fiveseven808/HueBerry_SmartSwitch/hueBerry Photos/B reel/IMG_20160812_172538.jpg

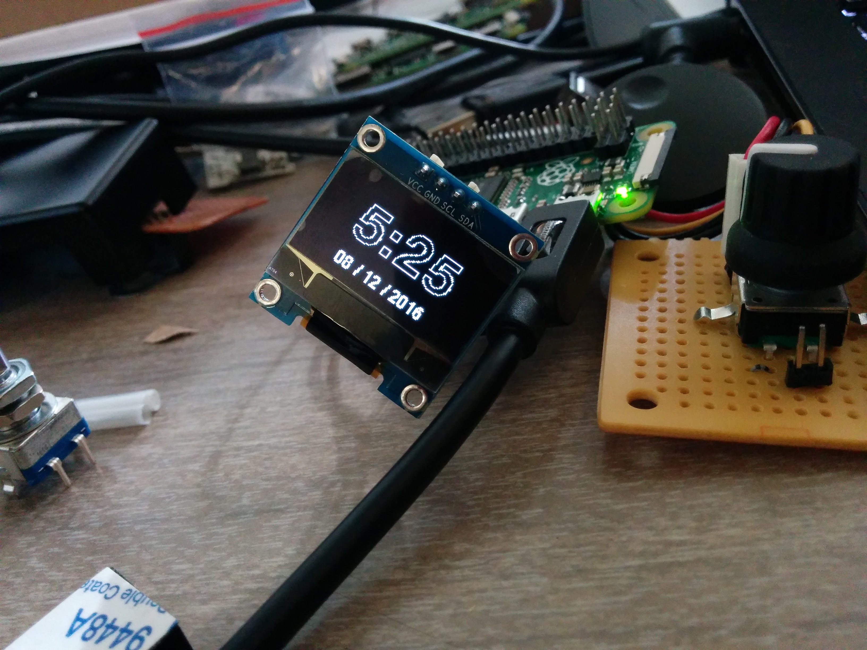
hueBerry Photos/B reel/IMG_20160812_172538.jpg
