fiveseven808/HueBerry_SmartSwitch/hueBerry Photos/B reel/IMG_20161223_000050.jpg

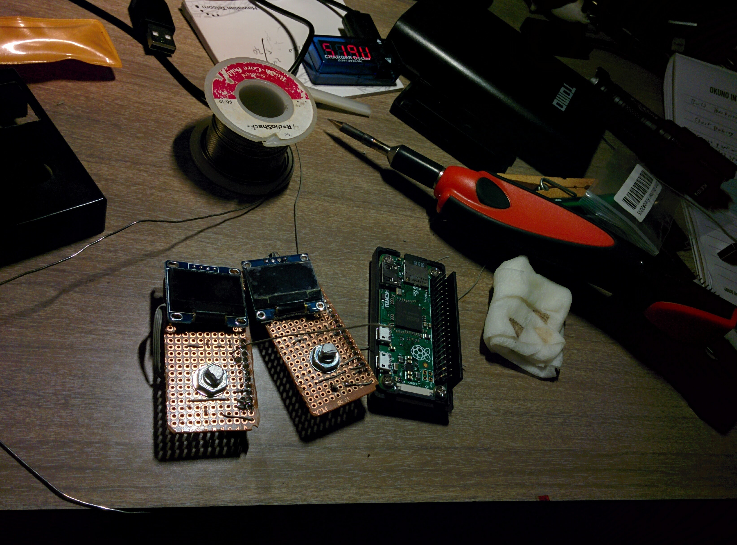
hueBerry Photos/B reel/IMG_20161223_000050.jpg
