fiveseven808/HueBerry_SmartSwitch/hueBerry Photos/B reel/IMG_20161223_075721.jpg

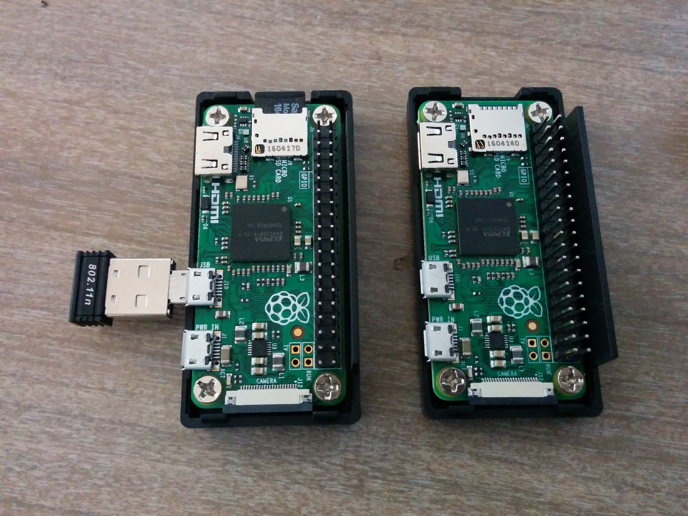
hueBerry Photos/B reel/IMG_20161223_075721.jpg
