fiveseven808/HueBerry_SmartSwitch/hueBerry Photos/Early Prototypes/IMG_20160802_123540.jpg

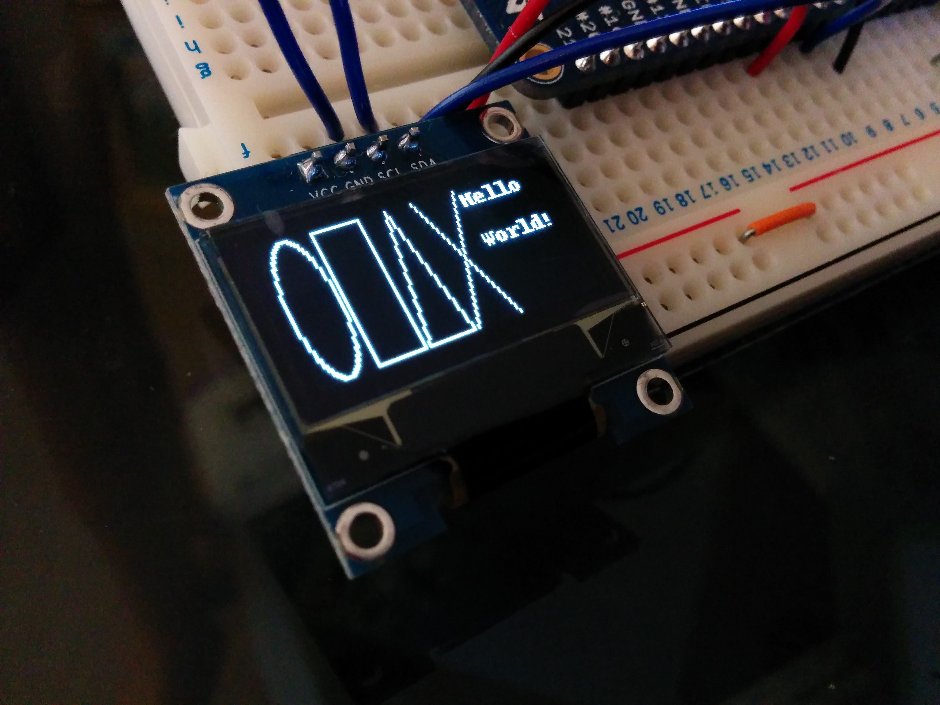
hueBerry Photos/Early Prototypes/IMG_20160802_123540.jpg
