fiveseven808/HueBerry_SmartSwitch/hueBerry Photos/Early Prototypes/IMG_20160812_081227.jpg

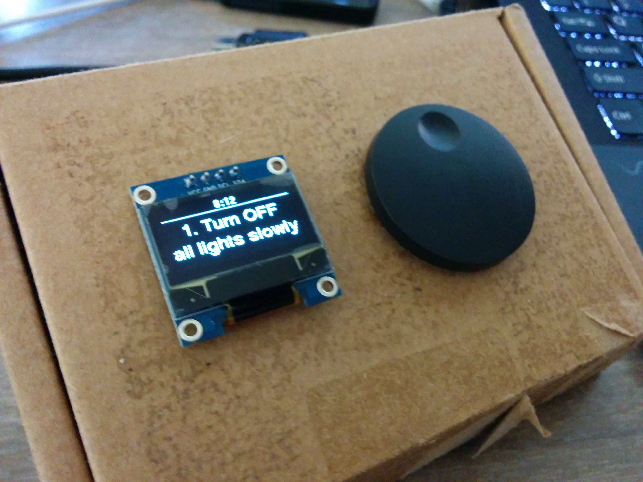
hueBerry Photos/Early Prototypes/IMG_20160812_081227.jpg
