fiveseven808/HueBerry_SmartSwitch/hueBerry Photos/Early Prototypes/IMG_20160812_081231.jpg

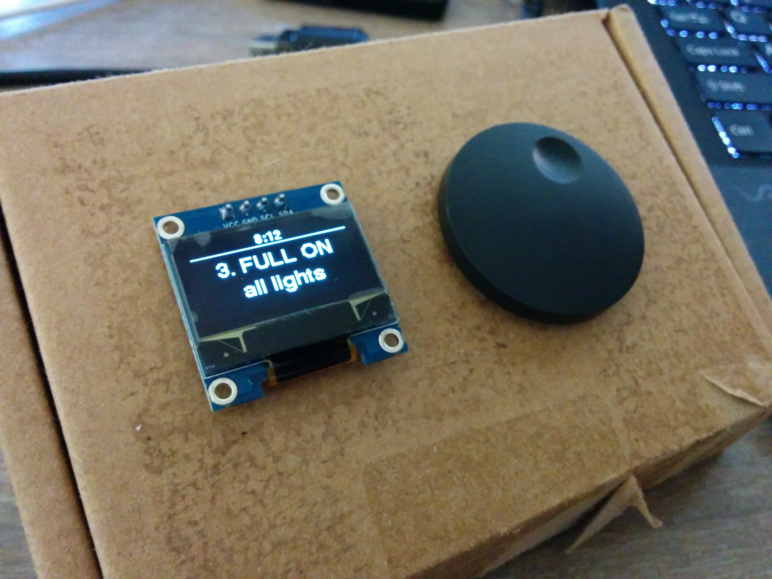
hueBerry Photos/Early Prototypes/IMG_20160812_081231.jpg
