fiveseven808/HueBerry_SmartSwitch/hueBerry Photos/Early Prototypes/IMG_20160812_081238.jpg

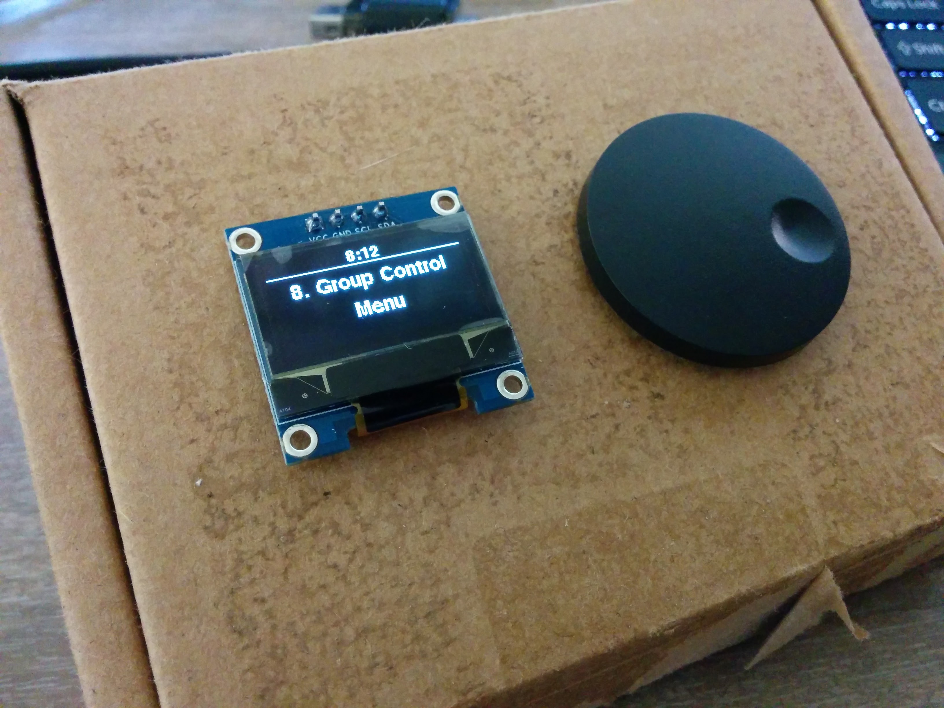
hueBerry Photos/Early Prototypes/IMG_20160812_081238.jpg
