fiveseven808/HueBerry_SmartSwitch/hueBerry Photos/Mistakes/FriedDisplay.jpg

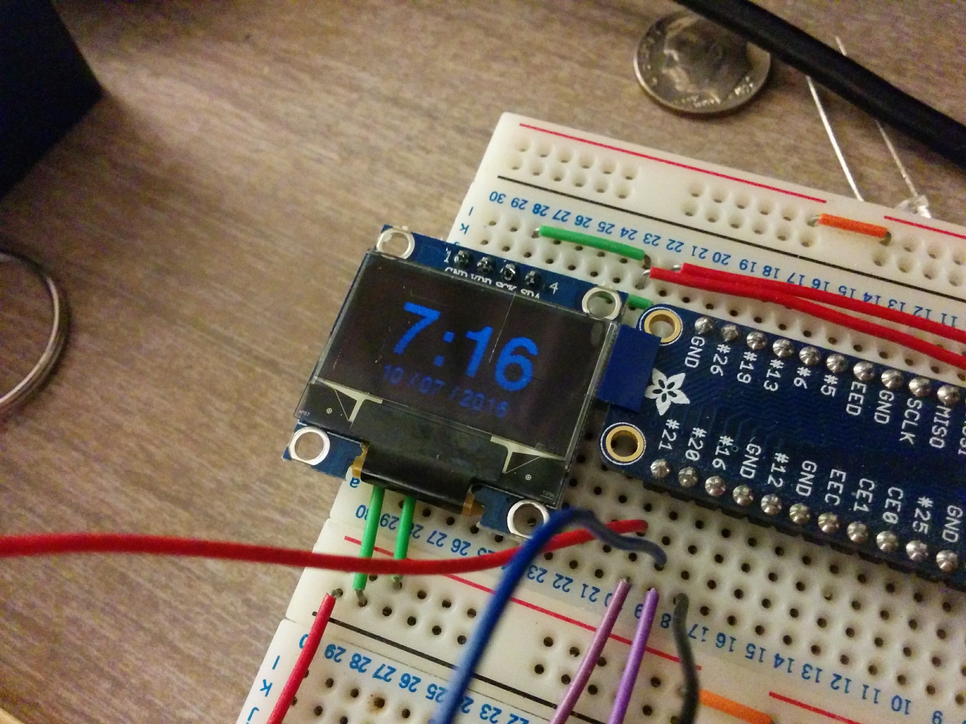
hueBerry Photos/Mistakes/FriedDisplay.jpg
