fiveseven808/HueBerry_SmartSwitch/hueBerry Photos/Mistakes/Notliketheothers.jpg

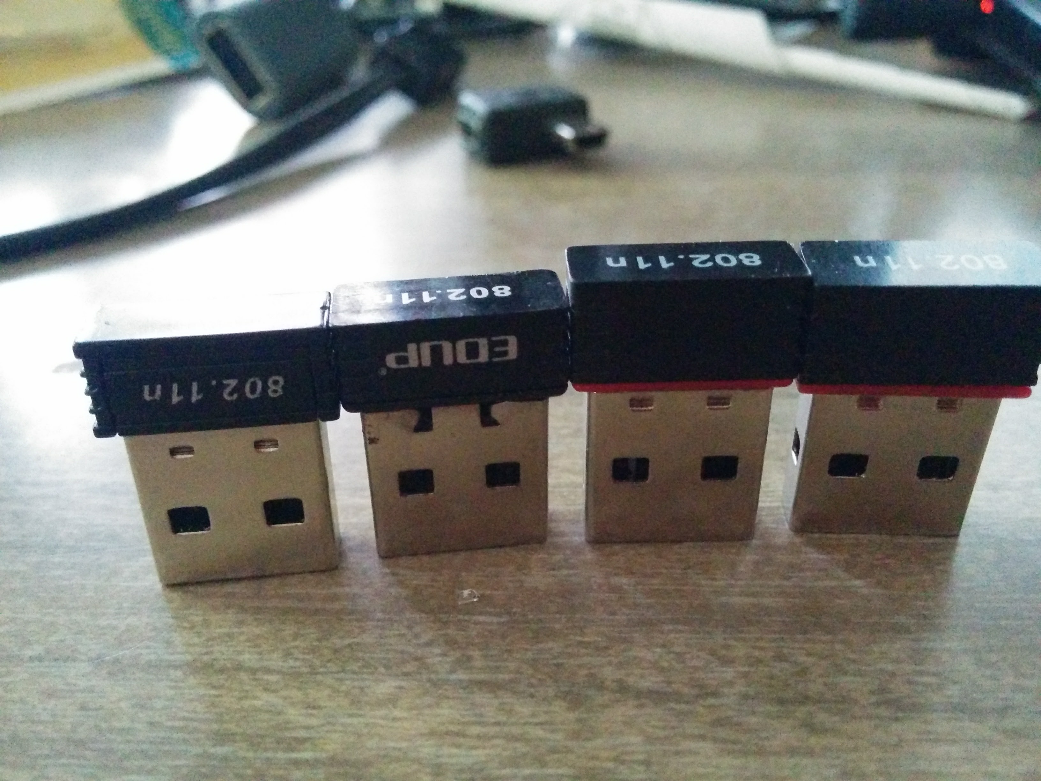
hueBerry Photos/Mistakes/Notliketheothers.jpg
