fiveseven808/HueBerry_SmartSwitch/hueBerry Photos/Construction/IMG_20160925_205256.jpg

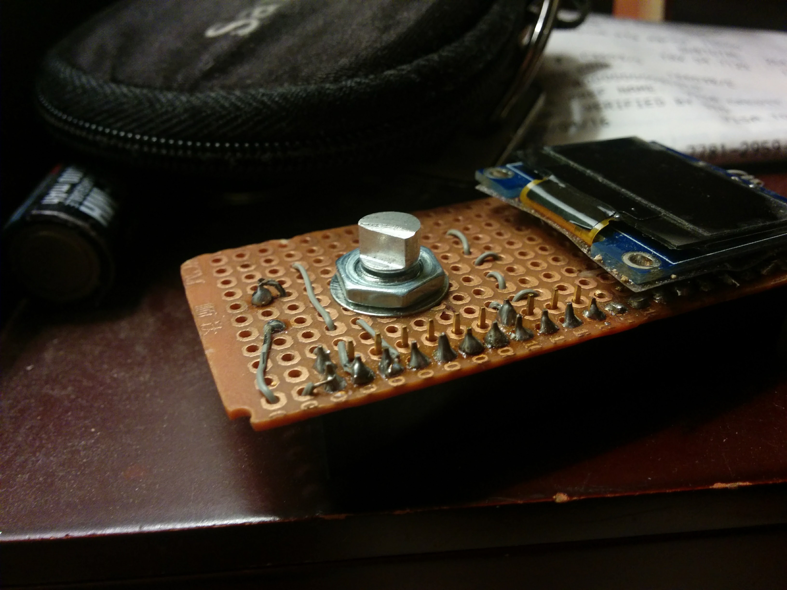
hueBerry Photos/Construction/IMG_20160925_205256.jpg
