fiveseven808/HueBerry_SmartSwitch/hueBerry Photos/Battery Test/IMG_20160907_173014.jpg

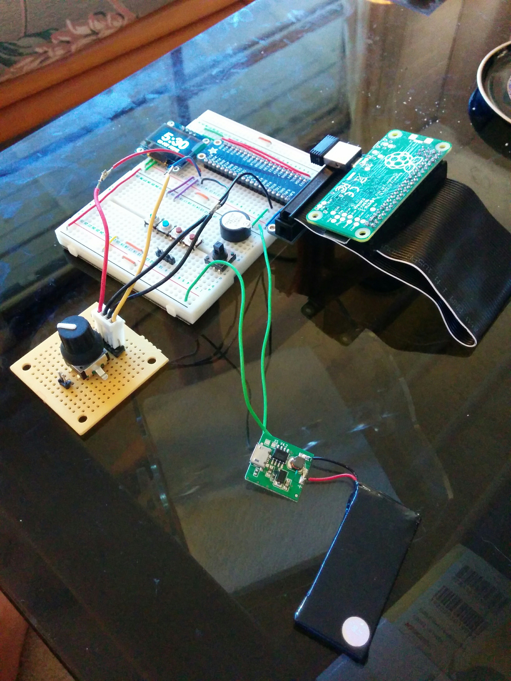
hueBerry Photos/Battery Test/IMG_20160907_173014.jpg
