fiveseven808/HueBerry_SmartSwitch/v032.py

#!/usr/bin/env python
"""
v032
2017 0127
looks like scene saving is working good. Goona go and rearrange my hard scenes to be at the end. 
gonna make custom scenes configurable. make a transition time gathering thing. 
remeoved scene by group since by light is so fast
new process:
    select a scene
        click to activate scene
    hold down for 5 seconds to edit scene
        new menu:
        record scene
        edit transition time
        
    

v031
2017 0126
adding the scene creation function. and replay. 
added 2 ways to do it. using the per light way. both ways work actually. may lead to interesting results
fuck this was difficult 
    

v030 UNTESTED
2017 0118
adding debug statements to each main menu item and light and group action so i can figure out what calvin is doing 

v029 
2017 0116
added keyvalues array to the get_hue_groups function so now we know what the group IDs are specificaLLY 
updated hue control to have full saturation to make it easier to figure out what color you want without having to adjust saturation first. 
updated get_group_names to use the new json scheme 

v028
20170108
removing group 5 from turn on all lights
added debug function and trying to figure out calvins problem
added error handling for hue lights and hue groups function in case calvins thing freaks out 
added proper failed return values so it fails gracefully


v027
20170106 1025
changing display dimish time to 9pm on both date and time

v026
20170103 1117
adding error handlig to the light functions so they dont crash when viewing a group that has no bulbs or a nonexistant group 

v025
20161227 1119
changed the dev info screen to scroll instead of button push. made the hue info screen it's own seperate thing to help curb freezing
added provisions for future upgrades
    - drop upgrade.py in the boot partition, and reboot. should detect and run as root (lol vulnerabilities)

--------------------
bug:
--------------------
philips hue bug
need to repair when no bridge found

search and test auth?
ping on startup?

check for response?
nothing found? 
"""
import os
import os.path
#set working directory to script directory
os.chdir(os.path.dirname(os.path.abspath(__file__)))
os.popen("python splashscreen.py &")
import threading
import time
import Adafruit_SSD1306
import RPi.GPIO as GPIO
from PIL import Image
from PIL import ImageFont
from PIL import ImageDraw
import pigpio
import rotary_encoder
import authenticate
import json
#import subprocess
#import huepi
#figure out how to export this to huepi

global logfile
logfile = "/home/pi/hueberry.log"

menu_timeout = 30 #seconds



#--------------------------------------------------------------------------
def get_group_names():
    result_array = []
    lstate_a = []
    #display_2lines("starting","group names",17)
    #debugmsg("starting curl")
    os.popen("curl -H \"Accept: application/json\" -X GET " + api_url + "/groups  > groups")
    #debugmsg("finished curl")
    #display_2lines("finished","curl",17)
    cmdout = os.popen("cat groups").read()
    #debugmsg(cmdout)
    if not cmdout:
        #print "not brite"
        display_2lines("An error in ","get_group_names",15)
        debugmsg("error in get_group_names probably lost connection to hub")
        time.sleep(2)
        return 0,0,0,0
    #debugmsg("passed ifstatement")
    #print cmdout
    #os.popen("rm groups")
    wat = json.loads(cmdout)
    keyvalues =  wat.keys()
    #print keyvalues
    for x, v  in wat.items():
        result_array.append(wat[x]['name'])
        lstate_a.append(wat[x]['action']['on'])
    num_groups = len(result_array)
    #print num_groups
    #print result_array
    arraysize = len(keyvalues)
    return result_array,num_groups,lstate_a,keyvalues

def get_light_names():
    os.popen("curl -H \"Accept: application/json\" -X GET " + api_url + "/lights  > lights")
    light_names = os.popen("cat lights | grep -P -o '\"name\":\".*?\"' | grep -o ':\".*\"' | tr -d '\"' | tr -d ':'").read()
    if not light_names:
        #print "not brite"
        display_2lines("An error in ","get_light_names",15)
        debugmsg("error in get_light_names probably lost connection to hub")
        time.sleep(2)
        return 0,0,0,0,0
    num_lights = os.popen("cat lights | grep -P -o '\"[0-9]*?\"' | tr -d '\"'").read()
    lstate = os.popen("cat lights | grep -o '\"on\":true,\|\"on\":false,' | tr -d '\"on\":' | tr -d ','").read()
    #os.popen("rm lights")
    name_array = light_names.split('\n')
    num_array = num_lights.split('\n')
    lstate_a = lstate.split('\n')
    total = len(num_array) - 1
    return name_array,num_array,lstate_a,total

    
def get_house_scene_by_light(scenenumber,ltt):
    #Get a fresh groups json file
    display_2lines("Grabbing","Light States",15)
    get_light_names() 
    #display_custom("ran get light names")
    cmdout = os.popen("cat lights").read()
    #os.popen("cat scene_template.py >> custom_scene" + scenenumber + ".py" )
    wat = json.loads(cmdout)
    #display_custom("used jsonloads")
    keyvalues =  wat.keys()
    arraysize = len(keyvalues)
    lstate_a = []
    result_array = []
    bri_array = []
    cmode_array = []
    hue_array = []
    ct_array = []
    sat_array = []
    xy_array = [] 
    #display_custom("blanked varliables")
    #time.sleep(3)
    for x, v  in wat.items():
            result_array.append(wat[x]['name'])
            lstate_a.append(wat[x]['state']['on'])
            #debugmsg v
    display_custom("ran first for")
    #time.sleep(3)
    for x, v  in wat.items():
        display_2lines("Building Array for","Light " + str(x) + " of " + str(len(result_array)),15)
        try:
            bri_array.append(wat[x]['state']['bri'])
        except:
            #debugmsg("errored on item " + x)
            bri_array.append("-1")
        try:
            cmode_array.append(wat[x]['state']['colormode'])
        except:
            #debugmsg("errored on item " + x)
            cmode_array.append("-1")
        try:
            hue_array.append(wat[x]['state']['hue'])
        except:
            #debugmsg("errored on item " + x)
            hue_array.append("-1")
        try:
            ct_array.append(wat[x]['state']['ct'])
        except:
            #debugmsg("errored on item " + x)
            ct_array.append("-1")
        try:
            sat_array.append(wat[x]['state']['sat'])
        except:
            #debugmsg("errored on item " + x)
            sat_array.append("-1")
        try:
            xy_array.append(wat[x]['state']['xy'])
        except:
            #debugmsg("errored on item " + x)
            xy_array.append("-1")
    #time.sleep(3)
    display_2lines("Array","built!",15)
    #print result_array
    #print lstate_a
    #print bri_array
    #print cmode_array
    #print hue_array
    #print ct_array
    #print sat_array
    #print xy_array        
    #ltt = 100
    #api_url = "http://testbridge/something"
    index = 0
    scenefile = str(scenenumber) + "_scene.sh"
    sceneobj = open(scenefile,"w+")
    sceneobj.write("#!/bin/bash\n#\n#This is a scenefile generated by hueBerry\n\n")
    display_2lines("Building","Scene Script!",15)
    while index < len(result_array):    
        scenecmd = "curl --silent -H \"Accept: application/json\" -X PUT --data '{\"on\":" + str(lstate_a[index]).lower() + ",\"bri\":" + str(bri_array[index]) + ",\"sat\":" + str(sat_array[index]) + ",\"xy\":" + str(xy_array[index]) + ",\"transitiontime\":" + str(ltt) + ",\"hue\":" + str(hue_array[index]) + "}' " + api_url + "/lights/" + str(keyvalues[index]) + "/state"
        #display_2lines("Writing","Lights " + str(index + 1) + " of " + str(len(result_array)),15)
        print(scenecmd)
        groupnum = index + 1
        sceneobj.write("echo \"Set Lights " + str(keyvalues[index]) + " = " + str(result_array[index]) + "\"\n")
        sceneobj.write(scenecmd + "\n")
        index += 1
    sceneobj.close
    os.popen("chmod a+x " + scenefile)
    display_2lines("Scenefile","Completed!",15)
    status = "completed"
    return status    
    
def hue_lights(lnum,lon,lbri,lsat,lx,ly,lct,ltt,**options):
    debugmsg("entering hue lights")
    if ('hue' in options):
        result = os.popen("curl --silent -H \"Accept: application/json\" -X PUT --data '{\"on\":" + str(lon) + ",\"bri\":" + str(lbri) + ",\"sat\":" + str(lsat) + ",\"xy\":[" + str(lx) + "," + str(ly) + "],\"transitiontime\":" + str(ltt) + ",\"hue\":" + str(options['hue']) + "}' " + api_url + "/lights/" + str(lnum) + "/state" ).read()
    else:
        result = os.popen("curl --silent -H \"Accept: application/json\" -X PUT --data '{\"on\":" + str(lon) + ",\"bri\":" + str(lbri) + ",\"sat\":" + str(lsat) + ",\"xy\":[" + str(lx) + "," + str(ly) + "],\"transitiontime\":" + str(ltt) + ",\"ct\":" + str(lct) + "}' " + api_url + "/lights/" + str(lnum) + "/state" ).read()
    debugmsg(result)    
    if not result:
        #print "not brite"
        display_2lines("An error in ","hue_lights",17)
        time.sleep(2)
        return
    print(result)
    return result

def hue_groups(lnum,lon,lbri,lsat,lx,ly,lct,ltt,**options):
    debugmsg("entering hue groups")
    if ('hue' in options):
        #debugmsg("hue and before result")
        result = os.popen("curl --silent -H \"Accept: application/json\" -X PUT --data '{\"on\":" + str(lon) + ",\"bri\":" + str(lbri) + ",\"sat\":" + str(lsat) + ",\"xy\":[" + str(lx) + "," + str(ly) + "],\"transitiontime\":" + str(ltt) + ",\"hue\":" + str(options['hue']) + "}' " + api_url + "/groups/" + str(lnum) + "/action" ).read()
        #debugmsg("hue and after result")
    else:
        #debugmsg("everything else and before result")
        result = os.popen("curl -s -m 1 -H \"Accept: application/json\" -X PUT --data '{\"on\":" + str(lon) + ",\"bri\":" + str(lbri) + ",\"sat\":" + str(lsat) + ",\"xy\":[" + str(lx) + "," + str(ly) + "],\"transitiontime\":" + str(ltt) + ",\"ct\":" + str(lct) + "}' " + api_url + "/groups/" + str(lnum) + "/action").read()
        #debugmsg("everything else and after result")
    debugmsg(result)
    if not result:
        #print "not brite"
        display_2lines("An error in ","hue_groups",17)
        time.sleep(2)
        return
    #print(result)
    #debugmsg("printed result")
    return result

#------------------------------------------------------------------------------------  
#   This function is the main menu for any light adjustment 
#   It displays lights or groups in the hue system and then allows you to control 
#       brightness, color temp, hue, and saturation in a fairly intuitive manner
#
#   Usage:
#       Specify "g" or "l" depending if you want to control a group or a light
#       Quick Push:
#           Brightness or exit
#       Long push:
#           CT adjustment or move to next option
#
#   Displays: 
#       Group or Light name as you scroll around. Allows you to change most attributes of the light
#------------------------------------------------------------------------------------
def light_control(mode):
    if (mode == "g"):
        display_custom("loading groups...")
        name_array,total,lstate_a,keyvalues = get_group_names()
    elif (mode == "l"):
        display_custom("loading lights...")
        name_array,num_lights,lstate_a,total = get_light_names()
    global pos
    old_display = 0
    refresh = 1
    exitvar = False
    menudepth = total + 1
    while exitvar == False:
        if(pos > menudepth):
            pos = menudepth
        elif(pos < 1):
            pos = 1
        display = pos

        #Display Selected Menu
        if (old_display != display or refresh == 1):
            if(display <= total):
                display_3lines(str(display) + ". " + str(name_array[display-1]),"Control","ON: " + str(lstate_a[display-1]),11,offset = 15)
            else:
                display_2lines("Back","One Level",17)
            old_display = display
            refresh = 0
        else:
            time.sleep(0.005)

        # Poll button press and trigger action based on current display
        if(not GPIO.input(21)):
            if(display <= total):
                ctmode = 0
                huemode = 0
                prev_mills = int(round(time.time() * 1000))
                while(not GPIO.input(21)):
                    mills = int(round(time.time() * 1000))
                    millsdiff = mills - prev_mills
                    if(millsdiff < 500):
                        display_custom("hold for ct...")
                    elif(millsdiff >= 500):
                        ctmode = 1
                        break
                while(not GPIO.input(21)):
                    display_custom("entering ct...")
                if(ctmode == 0):
                    if(mode == "g"):
                        g_control(keyvalues[display-1])
                        prev_mills = int(round(time.time() * 1000))
                        while(not GPIO.input(21)):
                            mills = int(round(time.time() * 1000))
                            millsdiff = mills - prev_mills
                            if(millsdiff < 500):
                                display_custom("hold for ct...")
                            elif(millsdiff >= 500):
                                ctmode = 1
                                break
                        if (ctmode ==0):
                            display_custom("returning...")
                        else:
                            while(not GPIO.input(21)):
                                display_custom("entering ct...")
                    elif(mode == "l"):
                        l_control(num_lights[display-1])
                        prev_mills = int(round(time.time() * 1000))
                        while(not GPIO.input(21)):
                            mills = int(round(time.time() * 1000))
                            millsdiff = mills - prev_mills
                            if(millsdiff < 500):
                                display_custom("hold for ct...")
                            elif(millsdiff >= 500):
                                ctmode = 1
                                break
                        if (ctmode ==0):
                            display_custom("returning...")
                        else:
                            while(not GPIO.input(21)):
                                display_custom("entering ct...")
                        

                if(ctmode == 1):
                    if(mode == "g"):
                        ct_control(keyvalues[display-1],"g")
                        prev_mills = int(round(time.time() * 1000))
                        while(not GPIO.input(21)):
                            mills = int(round(time.time() * 1000))
                            millsdiff = mills - prev_mills
                            if(millsdiff < 500):
                                display_custom("hold for hue...")
                            elif(millsdiff >= 500):
                                huemode = 1
                                break
                        if (huemode == 1):
                            hue_control(keyvalues[display-1],"g")
                            huemode = 0
                        elif(huemode ==0):
                            display_custom("returning...")
                        prev_mills = int(round(time.time() * 1000))
                        while(not GPIO.input(21)):
                            mills = int(round(time.time() * 1000))
                            millsdiff = mills - prev_mills
                            if(millsdiff < 500):
                                display_custom("hold for sat...")
                            elif(millsdiff >= 500):
                                huemode = 1
                                break
                        if (huemode == 1):
                            sat_control(keyvalues[display-1],"g")
                        elif(huemode ==0):
                            display_custom("returning...")
                           
                    elif(mode == "l"):
                        ct_control(num_lights[display-1],"l") 
                        prev_mills = int(round(time.time() * 1000))
                        while(not GPIO.input(21)):
                            mills = int(round(time.time() * 1000))
                            millsdiff = mills - prev_mills
                            if(millsdiff < 500):
                                display_custom("hold for hue...")
                            elif(millsdiff >= 500):
                                huemode = 1
                                break
                        if (huemode == 1):
                            hue_control(num_lights[display-1],"l")
                            huemode = 0
                        elif(huemode ==0):
                            display_custom("returning...")
                        prev_mills = int(round(time.time() * 1000))
                        while(not GPIO.input(21)):
                            mills = int(round(time.time() * 1000))
                            millsdiff = mills - prev_mills
                            if(millsdiff < 500):
                                display_custom("hold for sat...")
                            elif(millsdiff >= 500):
                                huemode = 1
                                break
                        if (huemode == 1):
                            sat_control(num_lights[display-1],"l")
                        elif(huemode ==0):
                            display_custom("returning...")
                if(mode == "g"):
                    name_array,total,lstate_a,keyvalues = get_group_names()
                elif(mode == "l"):
                    name_array,num_lights,lstate_a,total = get_light_names()
                refresh = 1 
                pos = display
            else:
                time.sleep(0.25)
                exitvar = True
            time.sleep(0.01)
            #prev_millis = int(round(time.time() * 1000))
    return
    


def g_control(group):
    display_custom("loading brightness...")
    os.popen("curl -H \"Accept: application/json\" -X GET " + api_url + "/groups/" + str(group) + " > brite")
    brite = os.popen("cat brite | grep -o '\"bri\":[0-9]*' | grep -o ':.*' | tr -d ':'").read()
    os.popen("rm brite")
    if not brite:
        #print "not brite"
        display_2lines("No devices","in group",17)
        time.sleep(3)
        return
    #else: 
    #    print "guess it was brite"
    brite = int(brite)      #make integer
    if brite < 10 and brite >= 0:
        brite = 10

    brite = brite/10        #trim it down to 25 values
    brite = int(brite)      #convert the float down to int agian
    global pos
    pos = brite
    exitvar = False
    max_rot_val = 25
    bri_pre = pos * 10
    refresh = 1
    prev_mills = 0 
    while exitvar == False:
        if(pos > max_rot_val):
            pos = max_rot_val
        elif(pos < 0):
            pos = 0
        mills = int(round(time.time() * 1000))
        millsdiff = mills - prev_mills
        rot_bri = pos * 10
        if(bri_pre != rot_bri or refresh ==  1 ):
            display_2lines("Group " + str(group),"Bri: " + str(int(rot_bri/2.5)) + "%",17)
            refresh = 0
        if rot_bri <= 0 and rot_bri != bri_pre:
            #hue_groups(lnum = group,lon = "false",lbri = rot_bri,lsat = "-1",lx = "-1",ly = "-1",ltt = "5", lct = "-1")
            huecmd = threading.Thread(target = hue_groups, kwargs={'lnum':group,'lon':"false",'lbri':rot_bri,'lsat':"-1",'lx':"-1",'ly':"-1",'ltt':"5",'lct':"-1"})
            huecmd.start()
            bri_pre = rot_bri
        elif(rot_bri != bri_pre and millsdiff > 200):
            #hue_groups(lnum = group,lon = "true",lbri = rot_bri,lsat = "-1",lx = "-1",ly = "-1",ltt = "5", lct = "-1")
            huecmd = threading.Thread(target = hue_groups, kwargs={'lnum':group,'lon':"true",'lbri':rot_bri,'lsat':"-1",'lx':"-1",'ly':"-1",'ltt':"5",'lct':"-1"})
            huecmd.start()
            bri_pre = rot_bri
            prev_mills = mills
        elif(millsdiff > 200): 
            prev_mills = mills
            
        if(not GPIO.input(21)):
            exitvar = True
        time.sleep(0.01)

#------------------------------------------------------------------------------------  
#   This function controls the color temperature of a light or group
#   Usage:
#       Specify the group or light ID in device
#       Specify "g" or "l" depending if you want to control a group or a light
#
#   Displays: 
#       Group or Light ID and current CT level in Kelvin 
#------------------------------------------------------------------------------------
def ct_control(device,mode):
    display_custom("loading ct...")
    if (mode == "g"):
        os.popen("curl -H \"Accept: application/json\" -X GET " + api_url + "/groups/" + str(device) + " > brite")
    elif (mode == "l"):
        os.popen("curl -H \"Accept: application/json\" -X GET " + api_url + "/lights/" + str(device) + " > brite")
    brite = os.popen("cat brite | grep -o '\"ct\":[0-9]*' | grep -o ':.*' | tr -d ':'").read()
    os.popen("rm brite")
    if not brite:
        #print "not brite"
        display_2lines("No devices","in group",17)
        time.sleep(3)
        return
    bri_length = len(brite)
    print bri_length
    if (bri_length > 0):
        brite = int(brite)      #make integer
        brite = 25-((brite - 153) / 14)
        brite = int(brite)      #convert the float down to int agian
    else:
        if (mode == "l"):
            display_custom("Light " + str(device) + " isn't CT-able")
        elif (mode == "g"):
            display_custom("Group " + str(device) + " isn't CT-able")
        time.sleep(.5)
        return
    global pos
    pos = brite
    exitvar = False
    max_rot_val = 25
    bri_pre = ((25-pos) * 14) + 153
    refresh = 1
    prev_mills = 0 
    while exitvar == False:
        if(pos > max_rot_val):
            pos = max_rot_val
        elif(pos < 0):
            pos = 0
        mills = int(round(time.time() * 1000))
        millsdiff = mills - prev_mills
        rot_bri = ((25-pos) * 14) + 153
        if(bri_pre != rot_bri or refresh ==  1 ):
            tempcalc = ((-12.968*rot_bri)+8484)/100
            tempcalc = (round(tempcalc))*100
            tempcalc = int(tempcalc)
            if(mode == "g"):
                display_2lines("Group " + str(device),"CT: " + str(int(tempcalc)) + "K",17)
            elif(mode == "l"):
                display_2lines("Light " + str(device),"CT: " + str(int(tempcalc)) + "K",17)
            refresh = 0
        if(rot_bri != bri_pre and millsdiff > 250):
            if(rot_bri > 500):
                rotbri = 500
            if(mode == "g"):
                #hue_groups(lnum = device,lon = "true",lbri = "-1",lsat = "-1",lx = "-1",ly = "-1",ltt = "5", lct = rot_bri)
                huecmd = threading.Thread(target = hue_groups, kwargs={'lnum':device,'lon':"true",'lbri':"-1",'lsat':"-1",'lx':"-1",'ly':"-1",'ltt':"5",'lct':rot_bri})
                huecmd.start()
            elif(mode == "l"):
                #hue_lights(lnum = device,lon = "true",lbri = "-1",lsat = "-1",lx = "-1",ly = "-1",ltt = "5", lct = rot_bri)
                huecmd = threading.Thread(target = hue_lights, kwargs={'lnum':device,'lon':"true",'lbri':"-1",'lsat':"-1",'lx':"-1",'ly':"-1",'ltt':"5",'lct':rot_bri})
                huecmd.start()
            bri_pre = rot_bri
            print rot_bri
            prev_mills = mills
        elif(millsdiff > 250): 
            prev_mills = mills
            
        if(not GPIO.input(21)):
            exitvar = True
        time.sleep(0.01)

def hue_control(device,mode):
    while(not GPIO.input(21)):
        display_custom("loading hue...")
    if (mode == "g"):
        os.popen("curl -H \"Accept: application/json\" -X GET " + api_url + "/groups/" + str(device) + " > brite")
    elif (mode == "l"):
        os.popen("curl -H \"Accept: application/json\" -X GET " + api_url + "/lights/" + str(device) + " > brite")
    brite = os.popen("cat brite | grep -o '\"hue\":[0-9]*' | grep -o ':.*' | tr -d ':'").read()
    os.popen("rm brite")
    if not brite:
        #print "not brite"
        display_2lines("No devices","in group",17)
        time.sleep(3)
        return
    bri_length = len(brite)
    print bri_length
    if (bri_length > 0):
        brite = int(brite)      #make integer
        brite = brite / 1310
        brite = int(round(brite))      #convert the float down to int agian
    else:
        print "something happened"
        if (mode == "l"):
            display_custom("Light " + str(device) + " isn't HUE-able")
        elif (mode == "g"):
            display_custom("Group " + str(device) + " isn't HUE-able")
        time.sleep(.5)
        return
    global pos
    pos = brite
    exitvar = False
    max_rot_val = 50
    bri_pre = brite
    refresh = 1
    prev_mills = 0 
    while exitvar == False:
        if(pos > max_rot_val):
            pos = 0
        elif(pos < 0):
            pos = max_rot_val   
        mills = int(round(time.time() * 1000))
        millsdiff = mills - prev_mills
        rot_bri = pos * 1310
        if(bri_pre != rot_bri or refresh ==  1 ):
            if(mode == "g"):
                display_2lines("Group " + str(device),"Hue: " + str(int(rot_bri)) ,17)
            elif(mode == "l"):
                display_2lines("Light " + str(device),"Hue: " + str(int(rot_bri)) ,17)
            refresh = 0
        if(rot_bri != bri_pre and millsdiff > 250):
            if(mode == "g"):
                #hue_groups(lnum = device,lon = "true",lbri = "-1",lsat = "-1",lx = "-1",ly = "-1",ltt = "5", lct = "-1", hue = rot_bri)
                huecmd = threading.Thread(target = hue_groups, kwargs={'lnum':device,'lon':"true",'lbri':"-1",'lsat':"250",'lx':"-1",'ly':"-1",'ltt':"5",'lct':"-1",'hue':rot_bri})
                huecmd.start()
            elif(mode == "l"):
                #hue_lights(lnum = device,lon = "true",lbri = "-1",lsat = "-1",lx = "-1",ly = "-1",ltt = "5", lct = "-1", hue = rot_bri)
                huecmd = threading.Thread(target = hue_lights, kwargs={'lnum':device,'lon':"true",'lbri':"-1",'lsat':"250",'lx':"-1",'ly':"-1",'ltt':"5",'lct':"-1",'hue':rot_bri})
                huecmd.start()
            bri_pre = rot_bri
            print rot_bri
            prev_mills = mills
        elif(millsdiff > 250): 
            prev_mills = mills
            
        if(not GPIO.input(21)):
            exitvar = True
        time.sleep(0.01)
        
def sat_control(device,mode):
    while(not GPIO.input(21)):
        display_custom("loading sat...")
    if (mode == "g"):
        os.popen("curl -H \"Accept: application/json\" -X GET " + api_url + "/groups/" + str(device) + " > brite")
    elif (mode == "l"):
        os.popen("curl -H \"Accept: application/json\" -X GET " + api_url + "/lights/" + str(device) + " > brite")
    brite = os.popen("cat brite | grep -o '\"sat\":[0-9]*' | grep -o ':.*' | tr -d ':'").read()
    os.popen("rm brite")
    if not brite:
        #print "not brite"
        display_2lines("No devices","in group",17)
        time.sleep(3)
        return
    bri_length = len(brite)
    print bri_length
    if (bri_length > 0):
        brite = int(brite)      #make integer
        brite = brite / 10
        brite = int(round(brite))      #convert the float down to int agian
    else:
        if (mode == "l"):
            display_custom("Light " + str(device) + " isn't SAT-able")
        elif (mode == "g"):
            display_custom("Group " + str(device) + " isn't SAT-able")
        time.sleep(.5)
        return
    global pos
    pos = brite
    exitvar = False
    max_rot_val = 25
    bri_pre = brite
    refresh = 1
    prev_mills = 0 
    while exitvar == False:
        if(pos > max_rot_val):
            pos = max_rot_val
        elif(pos < 0):
            pos = 0
        mills = int(round(time.time() * 1000))
        millsdiff = mills - prev_mills
        rot_bri = pos * 10
        if(bri_pre != rot_bri or refresh ==  1 ):
            if(mode == "g"):
                display_2lines("Group " + str(device),"Sat: " + str(int(rot_bri)) ,17)
            elif(mode == "l"):
                display_2lines("Light " + str(device),"Sat: " + str(int(rot_bri)) ,17)
            refresh = 0
        if(rot_bri != bri_pre and millsdiff > 250):
            if(mode == "g"):
                #hue_groups(lnum = device,lon = "true",lbri = "-1",lsat = rot_bri,lx = "-1",ly = "-1",ltt = "5", lct = "-1")
                huecmd = threading.Thread(target = hue_groups, kwargs={'lnum':device,'lon':"true",'lbri':"-1",'lsat':rot_bri,'lx':"-1",'ly':"-1",'ltt':"5",'lct':"-1"})
                huecmd.start()
            elif(mode == "l"):
                #hue_lights(lnum = device,lon = "true",lbri = "-1",lsat = rot_bri,lx = "-1",ly = "-1",ltt = "5", lct = "-1")
                huecmd = threading.Thread(target = hue_lights, kwargs={'lnum':device,'lon':"true",'lbri':"-1",'lsat':rot_bri,'lx':"-1",'ly':"-1",'ltt':"5",'lct':"-1"})
                huecmd.start()
            bri_pre = rot_bri
            print rot_bri
            prev_mills = mills
        elif(millsdiff > 250): 
            prev_mills = mills
            
        if(not GPIO.input(21)):
            exitvar = True
        time.sleep(0.01)
        
def l_control(light):
    display_custom("loading brightness...")
    os.popen("curl -H \"Accept: application/json\" -X GET  "+ api_url + "/lights/" + str(light) + " > brite")
    brite = os.popen("cat brite | grep -o '\"bri\":[0-9]*' | grep -o ':.*' | tr -d ':'").read()
    os.popen("rm brite")
    if not brite:
        #print "not brite"
        display_2lines("No devices","in lights",17)
        time.sleep(3)
        return
    brite = int(brite)      #make integer
    if brite < 10 and brite >= 0:
        brite = 10

    brite = brite/10        #trim it down to 25 values
    brite = int(brite)      #convert the float down to int agian
    global pos
    pos = brite
    exitvar = False
    max_rot_val = 25
    bri_pre = pos * 10
    refresh = 1
    prev_mills = 0 
    while exitvar == False:
        if(pos > max_rot_val):
            pos = max_rot_val
        elif(pos < 0):
            pos = 0
        mills = int(round(time.time() * 1000))
        millsdiff = mills - prev_mills
        rot_bri = pos * 10
        if(bri_pre != rot_bri or refresh == 1 ):
            display_2lines("Light " + str(light),"Bri: " + str(int(rot_bri/2.5)) + "%",17)
            refresh = 0 
        if rot_bri <= 0 and rot_bri != bri_pre:
            huecmd = threading.Thread(target = hue_lights, kwargs={'lnum':light,'lon':"false",'lbri':rot_bri,'lsat':"-1",'lx':"-1",'ly':"-1",'ltt':"5",'lct':"-1"})
            huecmd.start()
            bri_pre = rot_bri
        elif(rot_bri != bri_pre and millsdiff > 100):
            huecmd = threading.Thread(target = hue_lights, kwargs={'lnum':light,'lon':"true",'lbri':rot_bri,'lsat':"-1",'lx':"-1",'ly':"-1",'ltt':"5",'lct':"-1"})
            huecmd.start()
            bri_pre = rot_bri
            prev_mills = mills
        elif(millsdiff > 100): 
            prev_mills = mills

        if(not GPIO.input(21)):
            exitvar = True
        time.sleep(0.01)
#-------------------------------------------------------------------
#---------------Settings Menu and stuff-----------------------------
#-------------------------------------------------------------------
def pair_hue_bridge():
    pos = 0
    if os.path.isfile('./auth.json') == False:
        while True:
            display_3lines("Attempting Link","Push Bridge button" ,"Then push this button",11,offset = 15)
            if(not GPIO.input(21)):
                break
        display_custom("doing a thing...") 
        ip = authenticate.search_for_bridge()
        authenticate.authenticate('hueBerry',ip)
        authenticate.load_creds()
        api_key = authenticate.api_key
        bridge_ip = authenticate.bridge_ip
        display_2lines("Link Successful",bridge_ip,12)
        time.sleep(1)
    else:
        authenticate.load_creds()
        api_key = authenticate.api_key
        bridge_ip = authenticate.bridge_ip
        api_url = 'http://%s/api/%s' % (bridge_ip,api_key)
        display_2lines("Already Paired!",bridge_ip,12)
        time.sleep(1)
        
def devinfo_screen():
    time.sleep(.25)
    global pos
    pos = 0
    old_display = 0
    exitvar = False
    menudepth = 4
    refresh = 1 
    
    ipaddress = os.popen("ifconfig wlan0 | grep 'inet addr' | awk -F: '{print $2}' | awk '{print $1}'").read()
    ssid = os.popen("iwconfig wlan0 | grep 'ESSID' | awk '{print $4}' | awk -F\\\" '{print $2}'").read()
    ipaddress_0 = os.popen("ifconfig eth0 | grep 'inet addr' | awk -F: '{print $2}' | awk '{print $1}'").read()
    ipaddress_1 = os.popen("ifconfig eth1 | grep 'inet addr' | awk -F: '{print $2}' | awk '{print $1}'").read()
    while exitvar == False:
        if(pos > menudepth):
            pos = menudepth
        elif(pos < 1):
            pos = 1
        display = pos

        #Display Selected Menu
        if (old_display != display or refresh == 1):
            if(display == 1):
                display_3lines("hueBerry IP: " + str(ipaddress),"Bridge IP: " + str(bridge_ip) ,"WLAN SSID: " + str(ssid),9,offset = 15)
            elif(display == 2):
                display_3lines("eth0 IP: " + str(ipaddress_0),"eth1 IP: " + str(ipaddress_1) ,"blah",9,offset = 15)
            elif(display == 3):
                display_2lines("Get hue Hub","Info",17)
            else:
                display_2lines("Back to","Settings Menu",17)
            old_display = display
            refresh = 0 
        else:
            time.sleep(0.005)

        # Poll button press and trigger action based on current display
        if(not GPIO.input(21)):
            if(display == 1):
                ipaddress = os.popen("ifconfig wlan0 | grep 'inet addr' | awk -F: '{print $2}' | awk '{print $1}'").read()
                ssid = os.popen("iwconfig wlan0 | grep 'ESSID' | awk '{print $4}' | awk -F\\\" '{print $2}'").read()
                display_3lines("hueBerry IP: " + str(ipaddress),"Bridge IP: " + str(bridge_ip) ,"WLAN SSID: " + str(ssid),9,offset = 15)
            elif(display == 2):
                ipaddress_0 = os.popen("ifconfig eth0 | grep 'inet addr' | awk -F: '{print $2}' | awk '{print $1}'").read()
                ipaddress_1 = os.popen("ifconfig eth1 | grep 'inet addr' | awk -F: '{print $2}' | awk '{print $1}'").read()
                display_3lines("eth0 IP: " + str(ipaddress_0),"eth1 IP: " + str(ipaddress_1) ,"blah",9,offset = 15)
            elif(display == 3):
                get_hue_devinfo()
            else:
                time.sleep(0.25)
                exitvar = True
            refresh = 1
            pos = display
            while(not GPIO.input(21)):
                time.sleep(0.01)
            #prev_millis = int(round(time.time() * 1000))
    return
    
def get_hue_devinfo():
    display_custom("loading groups...")
    name_array,total,lstate_a,keyvalues = get_group_names()
    maxgroupid = keyvalues[total-1]
    display_custom("loading lights...")
    name_array,num_lights,lstate_a,total = get_light_names()
    maxlightid = num_lights[total-1]
    display_3lines("Max Light ID: " + str(maxlightid),"Max Group ID: " + str(maxgroupid) ,"something something",9,offset = 15)
    while True:
        time.sleep(0.01)
        if(not GPIO.input(21)):
            break
            
def shutdown_hueberry():
    display_3lines("Shutting down now...","Don't remove power" ,"Until Display is off",11,offset = 15)
    os.popen("sudo shutdown now")
    while True:
        time.sleep(1)
        
def restart_hueberry():
    display_3lines("Restarting now...","Don't remove power" ,"Please Wait",11,offset = 15)
    os.popen("sudo shutdown -r now")
    while True:
        time.sleep(1)
        
def flashlight_mode():
    while True:
        if(GPIO.input(21)):
            break
    draw.rectangle((0,0,width,height), outline=0, fill=1)
    disp.image(image)
    disp.display()
    while True:
        if(not GPIO.input(21)):
            break
        time.sleep(0.1)

def wifi_settings():
    display_custom("scanning for wifi...")
    global pos
    pos = 0
    timeout = 0 
    os.popen("wpa_cli scan")
    os.popen("wpa_cli scan_results | grep WPS | sort -r -k3 > /tmp/wifi")
    ssids = os.popen("cat /tmp/wifi | awk '{print $5}'").read()
    powers = os.popen("cat /tmp/wifi | awk '{print $3}'").read()
    macs = os.popen("cat /tmp/wifi | awk '{print $1}'").read()
    ssid_array = ssids.split('\n')
    mac_array = macs.split('\n')
    p_array = powers.split('\n')
    total = len(ssid_array) - 1
    menudepth = total + 1
    while True:
        if(pos > menudepth):
            pos = menudepth
        elif(pos < 0):
            pos = 0
        display = pos

        #Display Selected Menu
        if(display == 0):
            display_3lines("Scroll to see","Avaliable [WPS]" ,"SSIDs",11,offset = 15)
        elif(display <= total):
            display_3lines(str(display) + ". " + str(ssid_array[display-1]),"Signal: " + str(p_array[display-1]),"Connect ?",11,offset = 15)
        else:
            display_2lines("Back to","Settings Menu",17)

        # Poll button press and trigger action based on current display
        if(not GPIO.input(21)):
            if(display <= total and display > 0):
                timeout = 0
                display_3lines("Connecting To:",str(ssid_array[display-1]) ,"Push WPS button then click ",9,offset = 15)
                while True:
                    if(GPIO.input(21)):
                        break
                while True:
                    display_3lines("Connecting To:",str(ssid_array[display-1]) ,"Push WPS button then click ",9,offset = 15)
                    if(not GPIO.input(21)):
                        time.sleep(0.01)
                        break
                display_2lines("Pairing","Please Wait...",15)
                os.popen("wpa_cli wps_pbc " + str(mac_array[display-1]))
                # display_custom("something")
                time.sleep(2)
                while(timeout <= 60):
                    ipaddress = os.popen("ifconfig wlan0 | grep 'inet addr' | awk -F: '{print $2}' | awk '{print $1}'").read()
                    addr_len = len(ipaddress)
                    display_3lines("Waiting for an IP",".","IP: " + str(ipaddress),11,offset = 15)
                    if(addr_len > 4 ):
                        print("i have an ip address!!! at " + str(ipaddress))
                        break
                    timeout += 1
                    time.sleep(.25)
                    display_3lines("Waiting for an IP",". .","IP: " + str(ipaddress),11,offset = 15)
                    time.sleep(.25)
                    display_3lines("Waiting for an IP",". . .","IP: " + str(ipaddress),11,offset = 15)
                    time.sleep(.5)
                    if(not GPIO.input(21)):
                        break
                if(timeout >= 300):
                    display_2lines("Connection failed...","Try again",15)
                elif(addr_len < 4):
                    display_2lines("Connection canceled...","Try again",15)
                else:
                    display_2lines("Success!!!","IP: " + str(ipaddress),13)
                time.sleep(5)
            else:
                time.sleep(0.25)
                break
            time.sleep(0.01)
    
        
def settings_menu():
    time.sleep(.25)
    global pos
    pos = 0
    old_display = 0
    exitvar = False
    menudepth = 7
    refresh = 1 
    while exitvar == False:
        if(pos > menudepth):
            pos = menudepth
        elif(pos < 1):
            pos = 1
        display = pos

        #Display Selected Menu
        if (old_display != display or refresh == 1):
            if(display == 1):
                display_2lines(str(display) + ". Device","Info",17)
            elif(display == 2):
                display_2lines(str(display) + ". Re-Pair","Hue Bridge",17)
            elif(display == 3):
                display_2lines(str(display) + ". Shutdown","hueBerry",17)
            elif(display == 4):
                display_2lines(str(display) + ". Restart","hueBerry",17)
            elif(display == 5):
                display_2lines(str(display) + ". Flashlight","Function",17)
            elif(display == 6):
                display_2lines(str(display) + ". Connect to","WiFi",17)
            else:
                display_2lines("Back to","Main Menu",17)
            old_display = display
            refresh = 0 
        else:
            time.sleep(0.005)

        # Poll button press and trigger action based on current display
        if(not GPIO.input(21)):
            if(display == 1):
                devinfo_screen()
            elif(display == 2):
                os.popen("rm auth.json")
                pair_hue_bridge()
            elif(display == 3):
                shutdown_hueberry()
            elif(display == 4):
                restart_hueberry()
            elif(display == 5):
                flashlight_mode()
            elif(display == 6):
                wifi_settings()
            else:
                time.sleep(0.25)
                exitvar = True
            refresh = 1
            pos = display
            while(not GPIO.input(21)):
                time.sleep(0.01)
            #prev_millis = int(round(time.time() * 1000))
    return
        
#----------------------------------------------------------------------------

def display_time():
    # Collect current time and date
    if(time_format):
        current_time = time.strftime("%-I:%M")
    else:
        current_time = time.strftime("%-H:%M")

    current_date = time.strftime("%m / %d / %Y")

    # Clear image buffer by drawing a black filled box
    draw.rectangle((0,0,width,height), outline=0, fill=0)
    #Get 24 hour time variable
    H = int(time.strftime("%H"))
    # Set font type and size
    #H = 9
    if H >= 21 or H < 6:
        font = ImageFont.truetype('BMW_outline.otf', 40)
        #print("outline")
    else:
        font = ImageFont.truetype('BMW_naa.ttf', 45)
        #font = ImageFont.truetype('BMW_outline.otf', 40)
        #print("regular")
    #print H
    #time.sleep(100)

    # Position time
    x_pos = (disp.width/2)-(string_width(font,current_time)/2)
    y_pos = 2 + (disp.height-4-8)/2 - (35/2)

    # Draw time
    draw.text((x_pos, y_pos), current_time, font=font, fill=255)

    # Set font type and size
    font = ImageFont.truetype('BMW_naa.ttf', 13)
    #font = ImageFont.load_default()

    # Position date
    x_pos = (disp.width/2)-(string_width(font,current_date)/2)
    y_pos = disp.height-10

    # Draw date during daytime hours
    if H < 21 and H > 6:
        draw.text((x_pos, y_pos), current_date, font=font, fill=255)

    # Draw the image buffer
    disp.image(image)
    disp.display()

def display_2lines(line1,line2,size):
    # Clear image buffer by drawing a black filled box
    draw.rectangle((0,0,width,height), outline=0, fill=0)
    if(time_format):
        current_time = time.strftime("%-I:%M")
    else:
        current_time = time.strftime("%-H:%M")
    current_date = time.strftime("%m / %d / %Y")
    font = ImageFont.truetype('BMW_naa.ttf', 11)
    #font = ImageFont.load_default()
    #draw a clock
    # Position time
    x_pos = (disp.width/2)-(string_width(font,current_time)/2)
    y_pos = 0
    # Draw time
    draw.text((x_pos, y_pos), current_time, font=font, fill=255)
    #draw a menu line
    timeheight = 10
    draw.line((0, timeheight, disp.width, timeheight), fill=255)
    # Set font type and size
    font = ImageFont.truetype('BMW_naa.ttf', size)
    x_pos = (disp.width/2)-(string_width(font,line1)/2)
    y_pos = 8 + (disp.height-4-8)/2 - (35/2)
    draw.text((x_pos, y_pos), line1, font=font, fill=255)
    x_pos = (disp.width/2)-(string_width(font,line2)/2)
    y_pos = disp.height-26
    draw.text((x_pos, y_pos), line2, font=font, fill=255)
    disp.image(image)
    disp.display()

def display_3lines(line1,line2,line3,size,offset):
    # Clear image buffer by drawing a black filled box
    draw.rectangle((0,0,width,height), outline=0, fill=0)
    if(time_format):
        current_time = time.strftime("%-I:%M")
    else:
        current_time = time.strftime("%-H:%M")
    current_date = time.strftime("%m / %d / %Y")
    font = ImageFont.truetype('BMW_naa.ttf', 11)
    #font = ImageFont.load_default()
    #draw a clock
    # Position time
    x_pos = (disp.width/2)-(string_width(font,current_time)/2)
    y_pos = 0
    # Draw time
    draw.text((x_pos, y_pos), current_time, font=font, fill=255)
    #draw a menu line
    timeheight = 10
    draw.line((0, timeheight, disp.width, timeheight), fill=255)

    # Set font type and size
    font = ImageFont.truetype('BMW_naa.ttf', size)
    x_pos = (disp.width/2)-(string_width(font,line1)/2)
    y_pos = 8 + (disp.height-4-8)/2 - (35/2)
    draw.text((x_pos, y_pos), line1, font=font, fill=255)
    x_pos = (disp.width/2)-(string_width(font,line2)/2)
    y_pos += offset
    draw.text((x_pos, y_pos), line2, font=font, fill=255)
    x_pos = (disp.width/2)-(string_width(font,line3)/2)
    y_pos += offset
    draw.text((x_pos, y_pos), line3, font=font, fill=255)
    disp.image(image)
    disp.display()


def display_custom(text):
	# Clear image buffer by drawing a black filled box
	draw.rectangle((0,0,width,height), outline=0, fill=0)

	# Set font type and size
	#font = ImageFont.truetype('FreeMono.ttf', 8)
	font = ImageFont.load_default()

	# Position SSID
	x_pos = (width/2) - (string_width(font,text)/2)
	y_pos = (height/2) - (8/2)

	# Draw SSID
	draw.text((x_pos, y_pos), text, font=font, fill=255)

	# Draw the image buffer
	disp.image(image)
	disp.display()

def string_width(fontType,string):
	string_width = 0

	for i, c in enumerate(string):
		char_width, char_height = draw.textsize(c, font=fontType)
		string_width += char_width

	return string_width
   
def long_press(message,pin):
    prev_mills = int(round(time.time() * 1000))
    while(not GPIO.input(pin)):
        mills = int(round(time.time() * 1000))
        millsdiff = mills - prev_mills
        if(millsdiff < 500):
            display_custom("hold for ct...")
        elif(millsdiff >= 500):
            ctmode = 1
            break

def check_wifi_file():
    ADDWIFIPATH ='/boot/add_wifi.txt'
    if os.path.exists(ADDWIFIPATH):
        display_3lines("Wifi Creds Detected","Loading File...","Click to continue",13,16)
        while True:
            time.sleep(0.01)
            if(not GPIO.input(21)):
                break
        ssids = os.popen("cat /boot/add_wifi.txt | awk '{print $1}'").read()
        ssid_array = ssids.split('\n')
        display_3lines("SSID: " + str(ssid_array[0]),"PSK: " + str(ssid_array[1]),"Continue?",11,offset = 15)
        while True:
            time.sleep(0.01)
            if(not GPIO.input(21)):
                break
        with open("/etc/wpa_supplicant/wpa_supplicant.conf", "a") as myfile:
            myfile.write("\nnetwork={\n\tssid=\"" + str(ssid_array[0]) + "\"\n\tpsk=\"" + str(ssid_array[1]) + "\"\n}\n")
        os.rename(ADDWIFIPATH,ADDWIFIPATH + ".added")
        display_3lines("Added to database!","Rebooting... ","Please Wait",13,16)
        os.popen("sudo shutdown -r now")
        while True:
            time.sleep(1)
            
def check_upgrade_file():
    ADDWIFIPATH ='/boot/upgrade.py'
    if os.path.exists(ADDWIFIPATH):
        display_3lines("New Firmware Detected","Loading File...","Click to continue",13,16)
        while True:
            time.sleep(0.01)
            if(not GPIO.input(21)):
                break
        display_3lines("Performing","Upgrade","Please Wait...",13,16)
        os.popen("python " + ADDWIFIPATH)
        while True:
            time.sleep(1)
            
def debugmsg(message):
    global logfile
    current_time = time.strftime("%m / %d / %Y %-H:%M")
    with open(logfile, "a") as myfile:
        myfile.write(current_time + " " + message + "\n")

#------------------------------------------------------------------------------------------------------------------------------
# Main Loop I think
# Set up GPIO with internal pull-up
GPIO.setmode(GPIO.BCM)
GPIO.setup(21, GPIO.IN, pull_up_down=GPIO.PUD_UP)
#GPIO.setup(4, GPIO.OUT)
#GPIO.output(4,1)
# 128x64 display with hardware I2C
disp = Adafruit_SSD1306.SSD1306_128_64(rst=24)
# Initialize library
disp.begin()
# Get display width and height
width = disp.width
height = disp.height
# Clear display
#disp.clear()
#disp.display()
# Create image buffer with mode '1' for 1-bit color
image = Image.new('1', (width, height))
# Load default font
font = ImageFont.load_default()
# Create drawing object
draw = ImageDraw.Draw(image)
#--------------------------------------------------
prev_millis = 0
display = 0
time_format = True

#--------------------------------------------------
#Search to see if an Upgrade file exists, if so, run it 
check_upgrade_file()
#--------------------------------------------------
#Search to see if an Add Wifi file exists, if so, add it then delete it. 
check_wifi_file()


#--------------------------------------------------
#Search to see if an api key exists, if not, get it. 
if os.path.isfile('./auth.json') == False:
    display_3lines("Initial Setup:","hueBerry is","not paired",13,16)
    time.sleep(5)
    while True:
        display_3lines("Attempting Link:","Push Bridge button" ,"Then push button below",11,offset = 15)
        if(not GPIO.input(21)):
            break
    display_custom("Pairing...") 
    ip = authenticate.search_for_bridge()
    authenticate.authenticate('hueBerry',ip)
    authenticate.load_creds()
    api_key = authenticate.api_key
    bridge_ip = authenticate.bridge_ip
    display_2lines("Link Successful!",bridge_ip,12)
    time.sleep(1)
else:
    authenticate.load_creds()
    api_key = authenticate.api_key
    bridge_ip = authenticate.bridge_ip
    api_url = 'http://%s/api/%s' % (bridge_ip,api_key)
    display_2lines("Link Established",bridge_ip,12)
    time.sleep(0.1)

#----------------- set variables---------------
global pos
pos = 0
timeout = 0 
displaytemp = 0 
prev_secs = 0
old_min = 60 
old_display = 0
refresh = 1 

def callback(way):
        global pos
        pos += way
        #print("pos={}".format(pos))

pi = pigpio.pi()
decoder = rotary_encoder.decoder(pi, 16, 20, callback)

debugmsg("-----------------------------")
debugmsg("Starting hueBerry program version " + __file__)

while True:

    # Cycle through different displays
    if(pos > 10):
        pos = 10
    elif(pos < 0):
        pos = 0
    display = pos
    #Display Selected Menu 
    if(display == 0):
        cur_min = int(time.strftime("%M"))
        if(old_min != cur_min or refresh == 1):
            display_time()
            old_min = cur_min
            refresh = 0
        timeout = 0
        #Sleep to conserve CPU Cycles
        time.sleep(0.01)
    if(old_display != display):   
        if(display == 1):
            display_2lines(str(display) + ". Turn OFF","all lights slowly",17)
        elif(display == 2):
            display_2lines(str(display) + ". DIM ON","Night lights",17)
        elif(display == 3):
            display_2lines(str(display) + ". FULL ON","all lights",17)
        elif(display == 4):
            display_2lines(str(display) + ". Turn OFF","all lights quickly",17)
        elif(display == 5):
            display_2lines(str(display) + ". Record by Light","Scene 1",13)
        elif(display == 6):
            display_2lines(str(display) + ". 5am","Wakeup",17)
        elif(display == 7):
            display_2lines(str(display) + ". Activate", "Scene 1",17)
        elif(display == 8):
            display_2lines(str(display) + ". Settings", "Menu",13)
        elif(display == 9):
            display_2lines(str(display) + ". Light Control", "Menu",13)
        elif(display == 10):
            display_2lines(str(display) + ". Group Control", "Menu",13)
        old_display = display
        old_min = 60
    elif(display != 0):
        time.sleep(0.005)
        old_min = 60
    
    secs = int(round(time.time())) 
    timeout_secs = secs - prev_secs 
    if(display != 0 and displaytemp != display): 
        prev_secs = secs
        displaytemp = display  
    elif(display != 0 and timeout_secs >= menu_timeout):
        pos = 0
        display_temp = 0 
    elif(display == 0):
        displaytemp = display 
    #if(display != 0):
    #    print timeout_secs
    
    # Poll button press and trigger action based on current display
    if(not GPIO.input(21)):
        if(display == 0):
            # Toggle between 12/24h format
            time_format =  not time_format
            refresh = 1 
            while(not GPIO.input(21)):
                time.sleep(0.01)
        elif(display == 1):
            # Turn off all lights
            display_2lines("Turning all","lights OFF slowly",12)
            #os.popen("sudo ifdown wlan0; sleep 5; sudo ifup --force wlan0")
            debug = os.popen("curl -H \"Accept: application/json\" -X PUT --data '{\"on\":false,\"transitiontime\":100}' " + api_url + "/groups/0/action").read()
            #print(debug)
            time.sleep(1)
            debugmsg("turning all lights off")
        elif(display == 2):
            # Turn on NIGHT lights dim (groups 1,2,3)
            display_2lines("Turning specific","lights on DIM",12)
            debug = os.popen("curl -H \"Accept: application/json\" -X PUT --data '{\"on\":false,\"bri\":1,\"transitiontime\":4}' " + api_url + "/groups/1/action").read()
            hue_lights(lnum = "8",lon = "true",lbri = "1",lsat = "1",lx = "-1",ly = "-1",ltt = "4", lct = "400")
            debug = os.popen("curl -H \"Accept: application/json\" -X PUT --data '{\"on\":false,\"bri\":1,\"transitiontime\":4}' " + api_url + "/groups/2/action").read()
            hue_lights(lnum = "5",lon = "true",lbri = "1",lsat = "200",lx = "0.5015",ly = "0.4153",ltt = "4", lct = "-1")
            debug = os.popen("curl -H \"Accept: application/json\" -X PUT --data '{\"on\":false,\"bri\":1,\"transitiontime\":4}' " + api_url + "/groups/3/action").read()
            hue_groups(lnum = "6",lon = "true",lbri = "1",lsat = "200",lx = "-1",ly = "-1",ltt = "4",lct = "400")
            # Turn off front door light
            #print(debug)
            time.sleep(.5)
            debugmsg("turning on night lights dim")
        elif(display == 3):
            display_2lines("Turning all","lights on FULL",12)
            hue_groups(lnum = "0",lon = "true",lbri = "254",lsat = "256",lx = "-1",ly = "-1",ltt = "4",lct = "-1")
            ##turn off front door light... we dont want that...
            #hue_groups(lnum = "5",lon = "false",lbri = "1",lsat = "256",lx = "-1",ly = "-1",ltt = "4",lct = "-1")
            debugmsg("turning all lights on full")
        elif(display == 4):
            display_2lines("Turning all","lights OFF quickly",12)
            hue_groups(lnum = "0",lon = "false",lbri = "256",lsat = "256",lx = "-1",ly = "-1",ltt = "4",lct = "-1")
            debugmsg("turning all lights off quick")
        elif(display == 5):
            scenenumber = 1
            ltt = 100
            #result = get_house_scene_by_group(scenenumber,ltt)
            result = get_house_scene_by_light(scenenumber,ltt)
            debugmsg("ran scene by group creation with result = " + result)
        elif(display == 6):
            display_2lines("Turning lights:","5am wakeup",12)
            os.popen("./5amwakeup_scene.sh")
            time.sleep(1)
            debugmsg("turning lights 5am wakeup")
        elif(display == 7):
            display_2lines("Turning lights:","Scene 1",12)
            os.popen("./1_scene.sh")
            time.sleep(1)
            debugmsg("turning lights scene1")
        elif(display == 8):
            pos = 0
            settings_menu()
        elif(display == 9):
            pos = 0
            light_control("l")
        elif(display == 10):
            pos = 0
            light_control("g")
        time.sleep(0.01)
        #prev_millis = int(round(time.time() * 1000))
        pos = 0

    #time.sleep(0.1)

    
