fiveseven808/HueBerry_SmartSwitch/Plugins/display_bechmark_util.py

#!/usr/bin/env python

# Copyright (c) 2014 Adafruit Industries
# Author: Tony DiCola
#
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
# THE SOFTWARE IS PROVIDED "AS IS", WITHOUT WARRANTY OF ANY KIND, EXPRESS OR
# IMPLIED, INCLUDING BUT NOT LIMITED TO THE WARRANTIES OF MERCHANTABILITY,
# FITNESS FOR A PARTICULAR PURPOSE AND NONINFRINGEMENT. IN NO EVENT SHALL THE
# AUTHORS OR COPYRIGHT HOLDERS BE LIABLE FOR ANY CLAIM, DAMAGES OR OTHER
# LIABILITY, WHETHER IN AN ACTION OF CONTRACT, TORT OR OTHERWISE, ARISING FROM,
# OUT OF OR IN CONNECTION WITH THE SOFTWARE OR THE USE OR OTHER DEALINGS IN
# THE SOFTWARE.
#import os
#bearing = os.path.dirname(os.path.abspath(__file__))
#bearing = bearing + "/../"
#-----------------------------
#----Begin Plugin stuff-------
import plugin.hbplugin
hbapi = plugin.hbplugin.HB_PAPI(debug = 0) #this program won't work in debug mode
#-----------------------------
#------End Plugin stuff-------

import math
import time

import Adafruit_GPIO.SPI as SPI
import Adafruit_SSD1306

from PIL import Image
from PIL import ImageFont
from PIL import ImageDraw


# Raspberry Pi pin configuration:
RST = 24
# Note the following are only used with SPI:
DC = 23
SPI_PORT = 0
SPI_DEVICE = 0

# Beaglebone Black pin configuration:
# RST = 'P9_12'
# Note the following are only used with SPI:
# DC = 'P9_15'
# SPI_PORT = 1
# SPI_DEVICE = 0

# 128x32 display with hardware I2C:
# disp = Adafruit_SSD1306.SSD1306_128_32(rst=RST)

# 128x64 display with hardware I2C:
disp = Adafruit_SSD1306.SSD1306_128_64(rst=RST)

# 128x32 display with hardware SPI:
# disp = Adafruit_SSD1306.SSD1306_128_32(rst=RST, dc=DC, spi=SPI.SpiDev(SPI_PORT, SPI_DEVICE, max_speed_hz=8000000))

# 128x64 display with hardware SPI:
#disp = Adafruit_SSD1306.SSD1306_128_64(rst=RST, dc=DC, spi=SPI.SpiDev(SPI_PORT, SPI_DEVICE, max_speed_hz=8000000))

# Initialize library.
disp.begin()

# Get display width and height.
width = disp.width
height = disp.height

# Clear display.
disp.clear()
disp.display()

# Create image buffer.
# Make sure to create image with mode '1' for 1-bit color.
image = Image.new('1', (width, height))

# Load default font.
font = ImageFont.load_default()

# Alternatively load a TTF font.  Make sure the .ttf font file is in the same directory as this python script!
# Some nice fonts to try: http://www.dafont.com/bitmap.php
# font = ImageFont.truetype('Minecraftia.ttf', 8)

# Create drawing object.
draw = ImageDraw.Draw(image)

# Define text and get total width.
#text = 'SSD1306 ORGANIC LED DISPLAY. THIS IS AN OLD SCHOOL DEMO SCROLLER!! GREETZ TO: LADYADA & THE ADAFRUIT CREW, TRIXTER, FUTURE CREW, AND FARBRAUSCH'
#text = 'omg dis faka is so stupid'
text = "hueBerry Display Benchmark Test!"
maxwidth, unused = draw.textsize(text, font=font)

# Set animation and sine wave parameters.
amplitude = height/4
offset = height/2 - 4
velocity = -2
startpos = width

# Animate text moving in sine wave.
print('Press Ctrl-C to quit.')
pos = startpos
fps = 0.01
prev_mills = 0
fpsstring = "calculating..."
init_mills = int(round(time.time() * 1000))
while True:
    # Clear image buffer by drawing a black filled box.
    draw.rectangle((0,0,width,height), outline=0, fill=0)
    # Enumerate characters and draw them offset vertically based on a sine wave.
    x = pos
    for i, c in enumerate(text):
        # Stop drawing if off the right side of screen.
        if x > width:
            break
        # Calculate width but skip drawing if off the left side of screen.
        if x < -10:
            char_width, char_height = draw.textsize(c, font=font)
            x += char_width
            continue
        # Calculate offset from sine wave.
        y = offset+math.floor(amplitude*math.sin(x/float(width)*2.0*math.pi))
        # Draw text.
        draw.text((x, y), c, font=font, fill=255)
        # Increment x position based on chacacter width.
        char_width, char_height = draw.textsize(c, font=font)
        x += char_width

    mills = int(round(time.time() * 1000))
    millsdiff = mills - prev_mills
    totalmills = mills - init_mills
    if(millsdiff > 1000):
        avgfps = fps/(totalmills/1000.0)
        fpsstring = "fps: "+str(avgfps)
        prev_mills = mills
    #if(totalmills > 5000):
    #    init_mills = mills
    #    fps = 0
        #print fps
    # Draw the image buffer.
    draw.text((0, 0), fpsstring, font=font, fill=255)
    disp.image(image)
    disp.display()
    fps = fps + 1
    # Move position for next frame.
    pos += velocity
    # Start over if text has scrolled completely off left side of screen.
    if pos < -maxwidth:
        pos = startpos
    # Pause briefly before drawing next frame.
    #time.sleep(0.1)
    encoder_pos, pushed = hbapi.get_state()
    if pushed == 1:
        break
